berkingcreator/Anatolia-Development-Board/Anatolia-G-Kart/anatolia-g-back.png

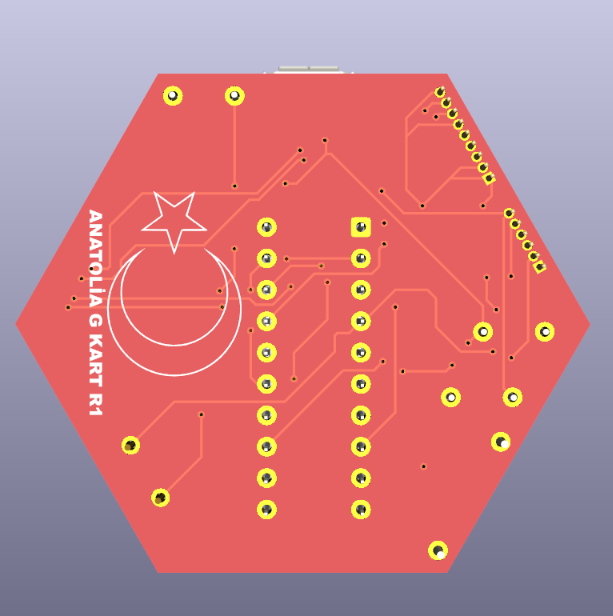
Anatolia-G-Kart/anatolia-g-back.png
