berkingcreator/Anatolia-Development-Board/Anatolia-G-Kart/anatolia-g.png

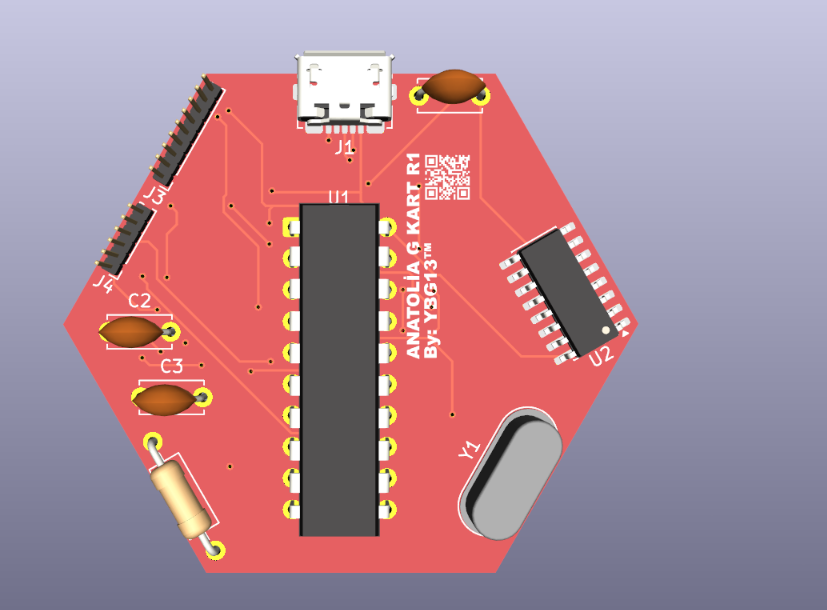
Anatolia-G-Kart/anatolia-g.png
