berkingcreator/Anatolia-Development-Board/Anatolia-Lite/anatolia-lite.png

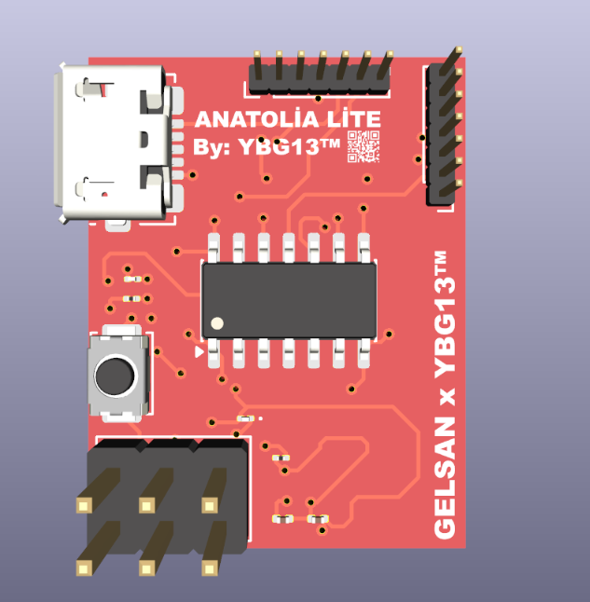
Anatolia-Lite/anatolia-lite.png
