berkingcreator/Anatolia-Development-Board/Anatolia-Micro-R2/anatolia-micro-r2-back.png

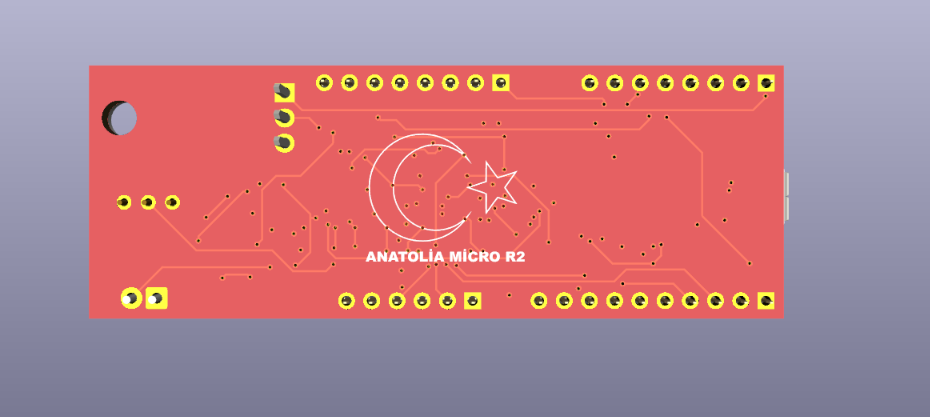
Anatolia-Micro-R2/anatolia-micro-r2-back.png
