berkingcreator/Anatolia-Development-Board/Anatolia-Micro-R2/anatolia-micro-r2.png

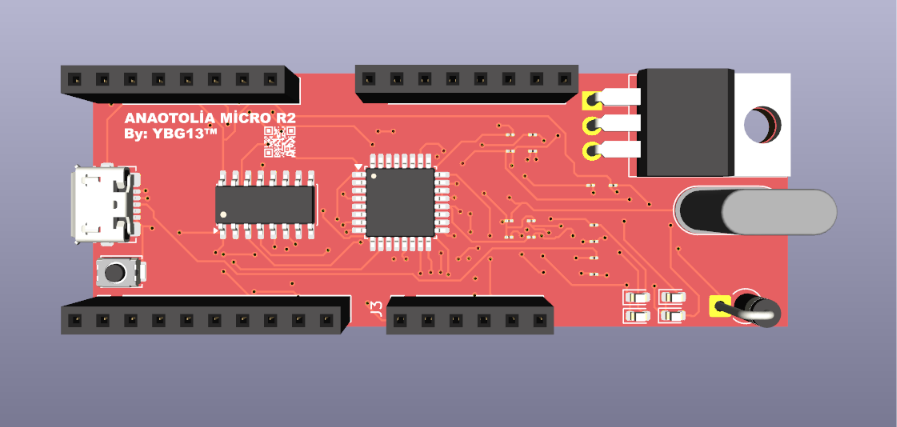
Anatolia-Micro-R2/anatolia-micro-r2.png
