berkingcreator/Anatolia-Development-Board/Anatolia-Pro-Mini/anatolia-pro-mini.png

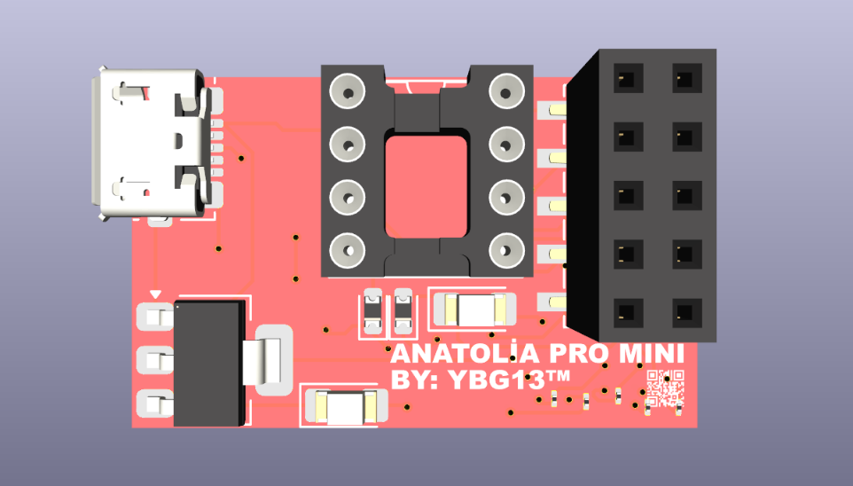
Anatolia-Pro-Mini/anatolia-pro-mini.png
