berkingcreator/Anatolia-Development-Board/Sensor/Rain-Sensor/rain-sensor-back.png

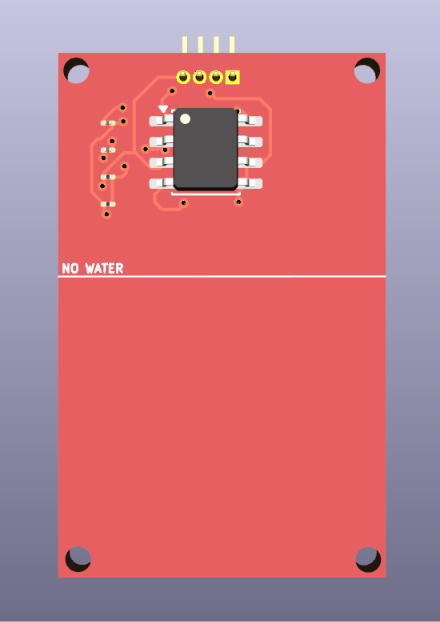
Sensor/Rain-Sensor/rain-sensor-back.png
